PaulKlasmann/Scraper-Blade-Sharpening-Jig/ScraperSharpeningJig_v1/Calibration_strip_8mm.FCStd

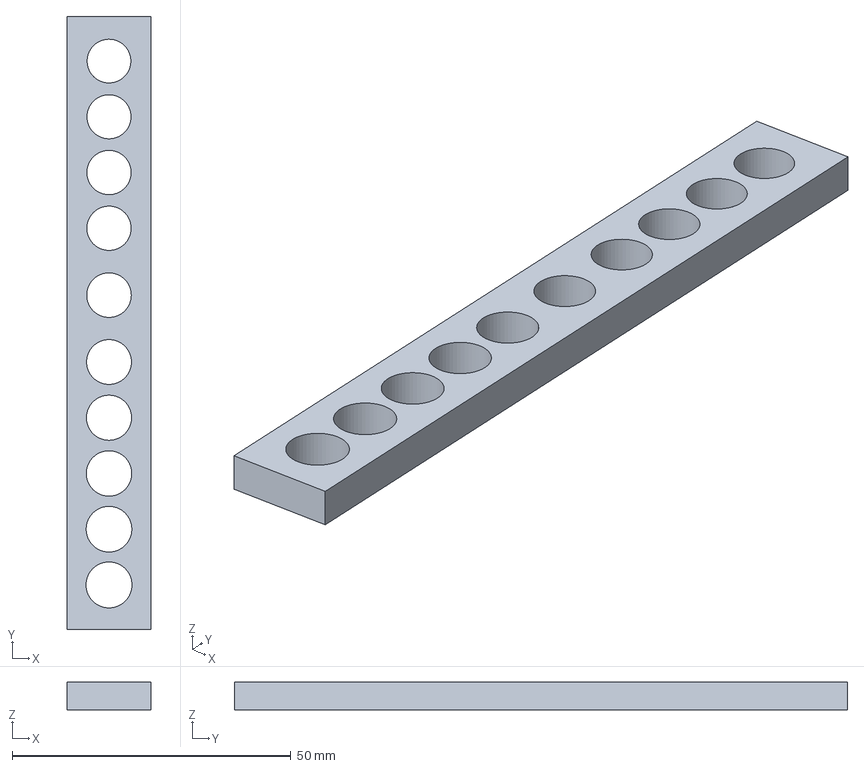
[picture p22: CAD file, 2026-07-06]
ScraperSharpeningJig_v1/Calibration_strip_8mm.FCStd
15.0 x 110.0 x 5.00 mm
